G-districts/CrowPanel-7.0-HMI-ESP32-Display-800x480/example/V1.0_and_V2.0/Arduino/arduino_code/7.0libraries/ESP32-audioI2S-master/examples/ESP32_A1S/AI-Thinker ESP32-Audio-Kit.jpg

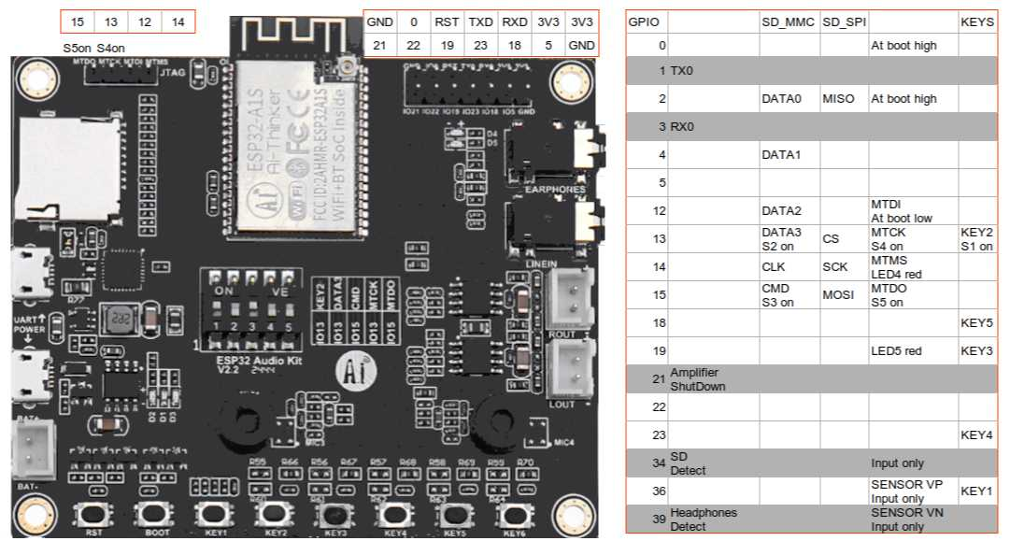
example/V1.0_and_V2.0/Arduino/arduino_code/7.0libraries/ESP32-audioI2S-master/examples/ESP32_A1S/AI-Thinker ESP32-Audio-Kit.jpg
