G-districts/CrowPanel-7.0-HMI-ESP32-Display-800x480/example/V1.0_and_V2.0/Arduino/arduino_code/7.0libraries/ESP32-audioI2S-master/examples/Simple_WiFi_Radio/Simple_WiFi_Radio_3.jpg

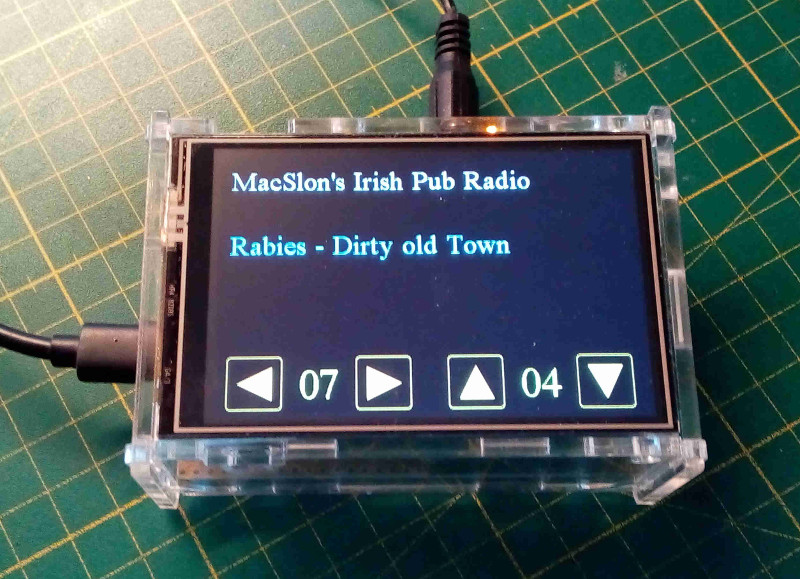
example/V1.0_and_V2.0/Arduino/arduino_code/7.0libraries/ESP32-audioI2S-master/examples/Simple_WiFi_Radio/Simple_WiFi_Radio_3.jpg
