G-districts/CrowPanel-7.0-HMI-ESP32-Display-800x480/example/V1.0_and_V2.0/HomeAssistant_7.0/7.0-inch_Squareline_Demo/README/2.png

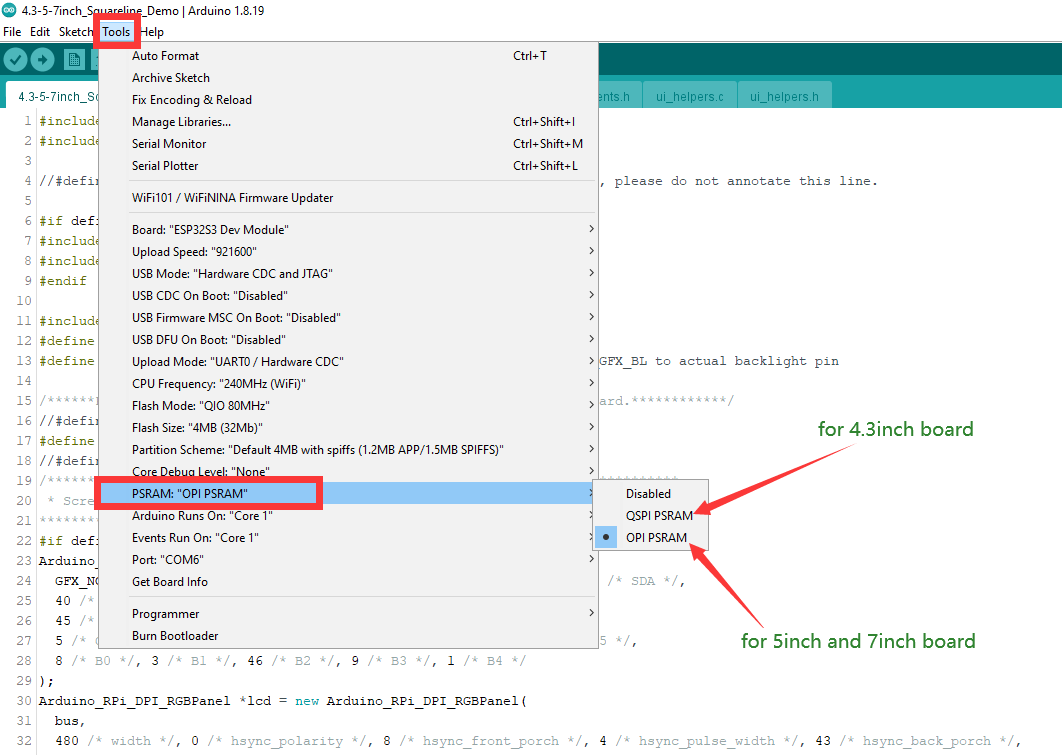
example/V1.0_and_V2.0/HomeAssistant_7.0/7.0-inch_Squareline_Demo/README/2.png
