G-districts/CrowPanel-7.0-HMI-ESP32-Display-800x480/example/V3.0/Micropython/SquareLine_Studio_Demo/LVGL-Assets-800x480/background1.png

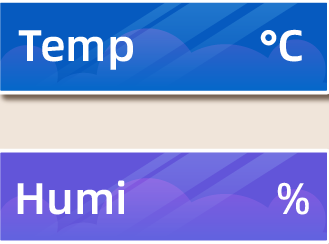
example/V3.0/Micropython/SquareLine_Studio_Demo/LVGL-Assets-800x480/background1.png
