G-districts/CrowPanel-7.0-HMI-ESP32-Display-800x480/example/V3.0/PlatformIO/LVGL-Assets-800x480/background.png

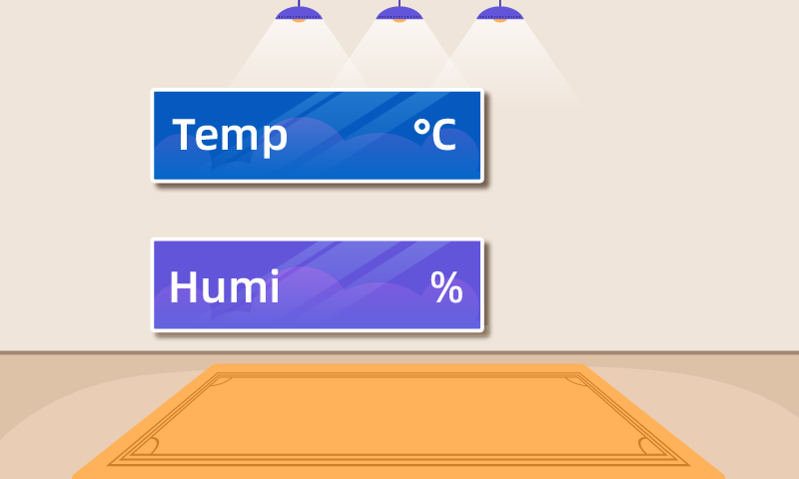
example/V3.0/PlatformIO/LVGL-Assets-800x480/background.png
