G-districts/CrowPanel-7.0-HMI-ESP32-Display-800x480/example/V3.0/ESP_IDF/LVGL_IDF/components/Arduino_GFX-master/examples/ImgViewer/ImgViewerBmp/data/octocatL.bmp

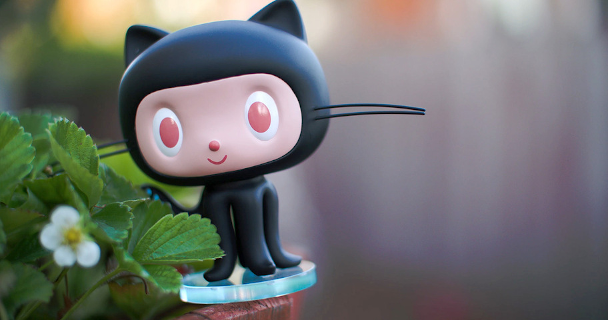
example/V3.0/ESP_IDF/LVGL_IDF/components/Arduino_GFX-master/examples/ImgViewer/ImgViewerBmp/data/octocatL.bmp
