G-districts/CrowPanel-7.0-HMI-ESP32-Display-800x480/example/V3.0/ESP_IDF/LVGL_IDF/components/Arduino_GFX-master/examples/ImgViewer/ImgViewerPng_PNGdec/data/octocat.png

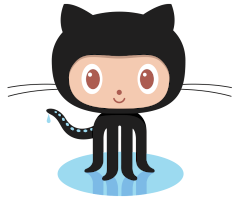
example/V3.0/ESP_IDF/LVGL_IDF/components/Arduino_GFX-master/examples/ImgViewer/ImgViewerPng_PNGdec/data/octocat.png
