G-districts/CrowPanel-7.0-HMI-ESP32-Display-800x480/example/V3.0/ESP_IDF/LVGL_IDF/components/Arduino_GFX-master/examples/ImgViewer/ImgViewerTiff_G4/data/at3_1m4_01_g4.tif

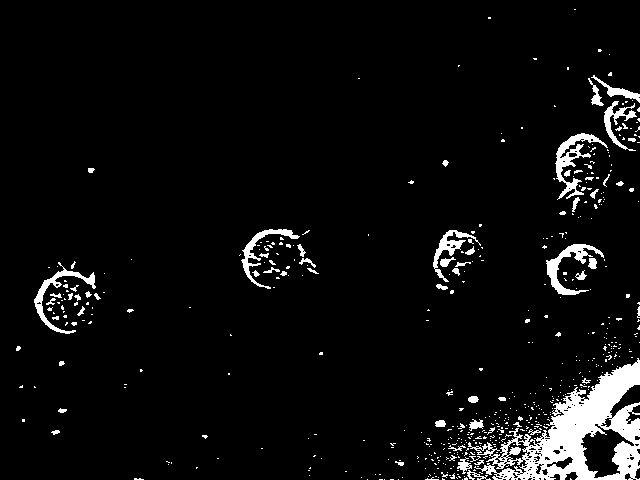
example/V3.0/ESP_IDF/LVGL_IDF/components/Arduino_GFX-master/examples/ImgViewer/ImgViewerTiff_G4/data/at3_1m4_01_g4.tif
