G-districts/CrowPanel-7.0-HMI-ESP32-Display-800x480/example/V3.0/ESP_IDF/LVGL_IDF/components/Arduino_GFX-master/examples/Sprite/SpriteGif/data/city17_240.gif

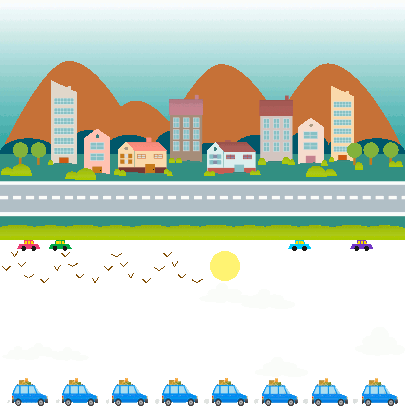
example/V3.0/ESP_IDF/LVGL_IDF/components/Arduino_GFX-master/examples/Sprite/SpriteGif/data/city17_240.gif
