G-districts/CrowPanel-7.0-HMI-ESP32-Display-800x480/example/V3.0/ESP_IDF/LVGL_IDF/components/Arduino_GFX-master/src/display/Arduino_RGB_Display.h

#pragma once

#include "../Arduino_DataBus.h"

//#if defined(ESP32) && (CONFIG_IDF_TARGET_ESP32S3)
#if defined(ESP32) && (CONFIG_IDF_TARGET_ESP32S3 || CONFIG_IDF_TARGET_ESP32P4)  //Modify

#include "../Arduino_GFX.h"
#include "../databus/Arduino_ESP32RGBPanel.h"

static const uint8_t gc9503v_type1_init_operations[] = {
    BEGIN_WRITE,
    WRITE_COMMAND_8, 0xF0,
    WRITE_BYTES, 5, 0x55, 0xAA, 0x52, 0x08, 0x00,

    WRITE_C8_D16, 0xF6, 0x5A, 0x87,

    WRITE_C8_D8, 0xC1, 0x3F,
    WRITE_C8_D8, 0xC2, 0x0E,
    WRITE_C8_D8, 0xC6, 0xF8,
    WRITE_C8_D8, 0xC9, 0x10,
    WRITE_C8_D8, 0xCD, 0x25,
    WRITE_C8_D8, 0xF8, 0x8A,
    WRITE_C8_D8, 0xAC, 0x45,
    WRITE_C8_D8, 0xA0, 0xDD,
    WRITE_C8_D8, 0xA7, 0x47,

    WRITE_COMMAND_8, 0xFA,
    WRITE_BYTES, 4, 0x00, 0x00, 0x00, 0x04,

    WRITE_C8_D8, 0xA3, 0xEE,

    WRITE_COMMAND_8, 0xFD,
    WRITE_BYTES, 3, 0x28, 0x28, 0x00,

    WRITE_C8_D8, 0x71, 0x48,
    WRITE_C8_D8, 0x72, 0x48,
    WRITE_C8_D16, 0x73, 0x00, 0x44,
    WRITE_C8_D8, 0x97, 0xEE,
    WRITE_C8_D8, 0x83, 0x93,
    WRITE_C8_D8, 0x9A, 0x72,
    WRITE_C8_D8, 0x9B, 0x5a,
    WRITE_C8_D16, 0x82, 0x2c, 0x2c,
    WRITE_C8_D8, 0xB1, 0x10,

    WRITE_COMMAND_8, 0x6D,
    WRITE_BYTES, 32,
    0x00, 0x1F, 0x19, 0x1A,
    0x10, 0x0e, 0x0c, 0x0a,
    0x02, 0x07, 0x1E, 0x1E,
    0x1E, 0x1E, 0x1E, 0x1E,
    0x1E, 0x1E, 0x1E, 0x1E,
    0x1E, 0x1E, 0x08, 0x01,
    0x09, 0x0b, 0x0D, 0x0F,
    0x1a, 0x19, 0x1f, 0x00,

    WRITE_COMMAND_8, 0x64,
    WRITE_BYTES, 16,
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

    WRITE_COMMAND_8, 0xEB,
    WRITE_BYTES, 7,
    0x02, 0x01, 0xE4, 0xE4,
    0x44, 0x00, 0x40,

    WRITE_C8_D16, 0xEC, 0x02, 0x01,

    WRITE_COMMAND_8, 0xED,
    WRITE_BYTES, 16,
    0xAB, 0x89, 0x76, 0x54,
    0x01, 0xFF, 0xFF, 0xFF,
    0xFF, 0xFF, 0xFF, 0x10,
    0x45, 0x67, 0x98, 0xBA,

    //-----------------------------------------End GIP Setting-----------------------------------------//
    //--------------------------- Power Control Registers Initial End------------------------------//
    //-------------------------------------Bank1 Setting------------------------------------------------//
    WRITE_COMMAND_8, 0xFF,
    WRITE_BYTES, 5, 0x77, 0x01, 0x00, 0x00, 0x00,

    WRITE_COMMAND_8, 0x21,   // 0x20 normal, 0x21 IPS
    WRITE_C8_D8, 0x3A, 0x77, // RGB 24bits D[23:0]

    WRITE_COMMAND_8, 0x11, // Sleep Out
    END_WRITE,

    DELAY, 100,

    BEGIN_WRITE,
    WRITE_COMMAND_8, 0x29, // Display On
    END_WRITE};

static const uint8_t st7701_type3_init_operations[] = {
    BEGIN_WRITE,
    WRITE_COMMAND_8, 0xFF,
    WRITE_BYTES, 5, 0x77, 0x01, 0x00, 0x00, 0x10,

    WRITE_C8_D16, 0xC0, 0x3B, 0x00,
    WRITE_C8_D16, 0xC1, 0x0B, 0x02, // VBP
    WRITE_C8_D16, 0xC2, 0x00, 0x02,
    WRITE_C8_D8, 0xCC, 0x10,
    WRITE_C8_D8, 0xCD, 0x08,

    WRITE_COMMAND_8, 0xB0, // Positive Voltage Gamma Control
    WRITE_BYTES, 16,
    0x02, 0x13, 0x1B, 0x0D,
    0x10, 0x05, 0x08, 0x07,
    0x07, 0x24, 0x04, 0x11,
    0x0E, 0x2C, 0x33, 0x1D,

    WRITE_COMMAND_8, 0xB1, // Negative Voltage Gamma Control
    WRITE_BYTES, 16,
    0x05, 0x13, 0x1B, 0x0D,
    0x11, 0x05, 0x08, 0x07,
    0x07, 0x24, 0x04, 0x11,
    0x0E, 0x2C, 0x33, 0x1D,

    // PAGE1
    WRITE_COMMAND_8, 0xFF,
    WRITE_BYTES, 5, 0x77, 0x01, 0x00, 0x00, 0x11,

    WRITE_C8_D8, 0xB0, 0x5d, // 5d
    WRITE_C8_D8, 0xB1, 0x43, // VCOM amplitude setting
    WRITE_C8_D8, 0xB2, 0x81, // VGH Voltage setting, 12V
    WRITE_C8_D8, 0xB3, 0x80,
    WRITE_C8_D8, 0xB5, 0x43, // VGL Voltage setting, -8.3V
    WRITE_C8_D8, 0xB7, 0x85,
    WRITE_C8_D8, 0xB8, 0x20,

    WRITE_C8_D8, 0xC1, 0x78,
    WRITE_C8_D8, 0xC2, 0x78,

    WRITE_C8_D8, 0xD0, 0x88,

    WRITE_COMMAND_8, 0xE0,
    WRITE_BYTES, 3, 0x00, 0x00, 0x02,

    WRITE_COMMAND_8, 0xE1,
    WRITE_BYTES, 11,
    0x03, 0xA0, 0x00, 0x00,
    0x04, 0xA0, 0x00, 0x00,
    0x00, 0x20, 0x20,

    WRITE_COMMAND_8, 0xE2,
    WRITE_BYTES, 12,
    0x00, 0x00, 0x00, 0x00,
    0x00, 0x00, 0x00, 0x00,
    0x00, 0x00, 0x00, 0x00,

    WRITE_COMMAND_8, 0xE3,
    WRITE_BYTES, 4, 0x00, 0x00, 0x11, 0x00,

    WRITE_C8_D16, 0xE4, 0x22, 0x00,

    WRITE_COMMAND_8, 0xE5,
    WRITE_BYTES, 16,
    0x05, 0xEC, 0xA0, 0xA0,
    0x07, 0xEE, 0xA0, 0xA0,
    0x00, 0x00, 0x00, 0x00,
    0x00, 0x00, 0x00, 0x00,

    WRITE_COMMAND_8, 0xE6,
    WRITE_BYTES, 4, 0x00, 0x00, 0x11, 0x00,

    WRITE_C8_D16, 0xE7, 0x22, 0x00,

    WRITE_COMMAND_8, 0xE8,
    WRITE_BYTES, 16,
    0x06, 0xED, 0xA0, 0xA0,
    0x08, 0xEF, 0xA0, 0xA0,
    0x00, 0x00, 0x00, 0x00,
    0x00, 0x00, 0x00, 0x00,

    WRITE_COMMAND_8, 0xEB,
    WRITE_BYTES, 7,
    0x00, 0x00, 0x40, 0x40,
    0x00, 0x00, 0x00,

    WRITE_COMMAND_8, 0xED,
    WRITE_BYTES, 16,
    0xFF, 0xFF, 0xFF, 0xBA,
    0x0A, 0xBF, 0x45, 0xFF,
    0xFF, 0x54, 0xFB, 0xA0,
    0xAB, 0xFF, 0xFF, 0xFF,

    WRITE_COMMAND_8, 0xEF,
    WRITE_BYTES, 6,
    0x10, 0x0D, 0x04, 0x08,
    0x3F, 0x1F,

    WRITE_COMMAND_8, 0xFF,
    WRITE_BYTES, 5, 0x77, 0x01, 0x00, 0x00, 0x13,

    WRITE_C8_D8, 0xEF, 0x08,

    WRITE_COMMAND_8, 0xFF,
    WRITE_BYTES, 5, 0x77, 0x01, 0x00, 0x00, 0x00,

    WRITE_COMMAND_8, 0x11, // Sleep Out
    END_WRITE,

    DELAY, 120,

    BEGIN_WRITE,
    WRITE_COMMAND_8, 0x29,   // Display On
    WRITE_COMMAND_8, 0x21,   // 0x20 normal, 0x21 IPS
    WRITE_C8_D8, 0x36, 0x00, // Display data access control
    WRITE_C8_D8, 0x3A, 0x60, // 0x60 18bit   0x50 16bit
    END_WRITE};

static const uint8_t st7701_type4_init_operations[] = {
    BEGIN_WRITE,

    WRITE_COMMAND_8, 0xFF,
    WRITE_BYTES, 5, 0x77, 0x01, 0x00, 0x00, 0x10,

    WRITE_C8_D16, 0xC0, 0x3b, 0x00,
    WRITE_C8_D16, 0xC1, 0x0b, 0x02,
    WRITE_C8_D16, 0xC2, 0x07, 0x02,
    WRITE_C8_D8, 0xCC, 0x10,
    WRITE_C8_D8, 0xCD, 0x08,

    WRITE_COMMAND_8, 0xB0, // Positive Voltage Gamma Control
    WRITE_BYTES, 16,
    0x00, 0x11, 0x16, 0x0e,
    0x11, 0x06, 0x05, 0x09,
    0x08, 0x21, 0x06, 0x13,
    0x10, 0x29, 0x31, 0x18,

    WRITE_COMMAND_8, 0xB1, // Negative Voltage Gamma Control
    WRITE_BYTES, 16,
    0x00, 0x11, 0x16, 0x0e,
    0x11, 0x07, 0x05, 0x09,
    0x09, 0x21, 0x05, 0x13,
    0x11, 0x2a, 0x31, 0x18,

    WRITE_COMMAND_8, 0xFF,
    WRITE_BYTES, 5, 0x77, 0x01, 0x00, 0x00, 0x11,

    WRITE_C8_D8, 0xb0, 0x6d,
    WRITE_C8_D8, 0xb1, 0x37,
    WRITE_C8_D8, 0xb2, 0x81,
    WRITE_C8_D8, 0xb3, 0x80,
    WRITE_C8_D8, 0xb5, 0x43,
    WRITE_C8_D8, 0xb7, 0x85,
    WRITE_C8_D8, 0xb8, 0x20,

    WRITE_C8_D8, 0xc1, 0x78,
    WRITE_C8_D8, 0xc2, 0x78,
    WRITE_C8_D8, 0xc3, 0x8c,

    WRITE_C8_D8, 0xd0, 0x88,

    WRITE_COMMAND_8, 0xe0,
    WRITE_BYTES, 3, 0x00, 0x00, 0x02,
    WRITE_COMMAND_8, 0xe1,
    WRITE_BYTES, 11,
    0x03, 0xa0, 0x00, 0x00,
    0x04, 0xa0, 0x00, 0x00,
    0x00, 0x20, 0x20,
    WRITE_COMMAND_8, 0xe2,
    WRITE_BYTES, 13,
    0x00, 0x00, 0x00, 0x00,
    0x00, 0x00, 0x00, 0x00,
    0x00, 0x00, 0x00, 0x00,
    0x00,
    WRITE_COMMAND_8, 0xe3,
    WRITE_BYTES, 4, 0x00, 0x00, 0x11, 0x00,
    WRITE_C8_D16, 0xe4, 0x22, 0x00,
    WRITE_COMMAND_8, 0xe5,
    WRITE_BYTES, 16,
    0x05, 0xec, 0xa0, 0xa0,
    0x07, 0xee, 0xa0, 0xa0,
    0x00, 0x00, 0x00, 0x00,
    0x00, 0x00, 0x00, 0x00,
    WRITE_COMMAND_8, 0xe6,
    WRITE_BYTES, 4, 0x00, 0x00, 0x11, 0x00,
    WRITE_C8_D16, 0xe7, 0x22, 0x00,
    WRITE_COMMAND_8, 0xe8,
    WRITE_BYTES, 16,
    0x06, 0xed, 0xa0, 0xa0,
    0x08, 0xef, 0xa0, 0xa0,
    0x00, 0x00, 0x00, 0x00,
    0x00, 0x00, 0x00, 0x00,
    WRITE_COMMAND_8, 0xeb,
    WRITE_BYTES, 7,
    0x00, 0x00, 0x40, 0x40,
    0x00, 0x00, 0x00,
    WRITE_COMMAND_8, 0xed,
    WRITE_BYTES, 16,
    0xff, 0xff, 0xff, 0xba,
    0x0a, 0xbf, 0x45, 0xff,
    0xff, 0x54, 0xfb, 0xa0,
    0xab, 0xff, 0xff, 0xff,
    WRITE_COMMAND_8, 0xef,
    WRITE_BYTES, 6,
    0x10, 0x0d, 0x04, 0x08,
    0x3f, 0x1f,
    WRITE_COMMAND_8, 0xff,
    WRITE_BYTES, 5, 0x77, 0x01, 0x00, 0x00, 0x13,
    WRITE_C8_D8, 0xef, 0x08,
    WRITE_COMMAND_8, 0xff,
    WRITE_BYTES, 5, 0x77, 0x01, 0x00, 0x00, 0x00,
    WRITE_C8_D8, 0x36, 0x08,
    WRITE_C8_D8, 0x3a, 0x66,
    WRITE_C8_D8, 0x11, 0x00,
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

    WRITE_C8_D8, 0xC1, 0x78,
    WRITE_C8_D8, 0xC2, 0x78,

    WRITE_C8_D8, 0xD0, 0x88,

    WRITE_C8_D8, 0xE0, 0x00,

    WRITE_C8_D8, 0x1B, 0x02,

    WRITE_COMMAND_8, 0xE1,
    WRITE_BYTES, 11,
    0x08, 0xA0, 0x00, 0x00,
    0x07, 0xA0, 0x00, 0x00,
    0x00, 0x44, 0x44,

    WRITE_COMMAND_8, 0xE2,
    WRITE_BYTES, 12,
    0x11, 0x11, 0x44, 0x44,
    0x75, 0xA0, 0x00, 0x00,
    0x74, 0xA0, 0x00, 0x00,

    WRITE_COMMAND_8, 0xE3,
    WRITE_BYTES, 4, 0x00, 0x00, 0x11, 0x11,

    WRITE_C8_D16, 0xE4, 0x44, 0x44,

    WRITE_COMMAND_8, 0xE5,
    WRITE_BYTES, 16,
    0x0A, 0x71, 0xD8, 0xA0,
    0x0C, 0x73, 0xD8, 0xA0,
    0x0E, 0x75, 0xD8, 0xA0,
    0x10, 0x77, 0xD8, 0xA0,

    WRITE_COMMAND_8, 0xE6,
    WRITE_BYTES, 4, 0x00, 0x00, 0x11, 0x11,

    WRITE_C8_D16, 0xE7, 0x44, 0x44,

    WRITE_COMMAND_8, 0xE8,
    WRITE_BYTES, 16,
    0x09, 0x70, 0xD8, 0xA0,
    0x0B, 0x72, 0xD8, 0xA0,
    0x0D, 0x74, 0xD8, 0xA0,
    0x0F, 0x76, 0xD8, 0xA0,

    WRITE_COMMAND_8, 0xEB,
    WRITE_BYTES, 7,
    0x02, 0x00, 0xE4, 0xE4,
    0x88, 0x00, 0x40,

    WRITE_C8_D16, 0xEC, 0x3C, 0x00,

    WRITE_COMMAND_8, 0xED,
    WRITE_BYTES, 16,
    0xAB, 0x89, 0x76, 0x54,
    0x02, 0xFF, 0xFF, 0xFF,
    0xFF, 0xFF, 0xFF, 0x20,
    0x45, 0x67, 0x98, 0xBA,

    WRITE_COMMAND_8, 0xEF,
    WRITE_BYTES, 6,
    0x08, 0x08, 0x08, 0x45,
    0x3F, 0x54,

    WRITE_COMMAND_8, 0xFF,
    WRITE_BYTES, 5, 0x77, 0x01, 0x00, 0x00, 0x13,

    WRITE_C8_D16, 0xE8, 0x00, 0x0E,

    WRITE_COMMAND_8, 0x20,   // 0x20 normal, 0x21 IPS
    WRITE_C8_D8, 0x3A, 0x50, // 0x70 RGB888, 0x60 RGB666, 0x50 RGB565

    WRITE_COMMAND_8, 0x11, // Sleep Out
    END_WRITE,

    DELAY, 150,

    BEGIN_WRITE,
    WRITE_C8_D16, 0xE8, 0x00, 0x0C,
    END_WRITE,

    DELAY, 100,

    BEGIN_WRITE,
    WRITE_C8_D16, 0xE8, 0x00, 0x00,

    WRITE_COMMAND_8, 0xFF,
    WRITE_BYTES, 5, 0x77, 0x01, 0x00, 0x00, 0x00,

    WRITE_COMMAND_8, 0x29, // Display On
    END_WRITE,
    DELAY, 20};

// Init code for 480x480 square (86 Box) GUITION ESP32-4848S040 display
static const uint8_t st7701_type9_init_operations[] = {
    BEGIN_WRITE,
    WRITE_COMMAND_8, 0xFF,
    WRITE_BYTES, 5, 0x77, 0x01, 0x00, 0x00, 0x10,

    WRITE_C8_D16, 0xC0, 0x3B, 0x00,
    WRITE_C8_D16, 0xC1, 0x0D, 0x02,
    WRITE_C8_D16, 0xC2, 0x31, 0x05,
    WRITE_C8_D8, 0xCD, 0x00, // changed by manufacture

    WRITE_COMMAND_8, 0xB0, // Positive Voltage Gamma Control
    WRITE_BYTES, 16,
    0x00, 0x11, 0x18, 0x0E,
    0x11, 0x06, 0x07, 0x08,
    0x07, 0x22, 0x04, 0x12,
    0x0F, 0xAA, 0x31, 0x18,

    WRITE_COMMAND_8, 0xB1, // Negative Voltage Gamma Control
    WRITE_BYTES, 16,
    0x00, 0x11, 0x19, 0x0E,
    0x12, 0x07, 0x08, 0x08,
    0x08, 0x22, 0x04, 0x11,
    0x11, 0xA9, 0x32, 0x18,

    // PAGE1
    WRITE_COMMAND_8, 0xFF,
    WRITE_BYTES, 5, 0x77, 0x01, 0x00, 0x00, 0x11,

    WRITE_C8_D8, 0xB0, 0x60, // Vop=4.7375v
    WRITE_C8_D8, 0xB1, 0x32, // VCOM=32
    WRITE_C8_D8, 0xB2, 0x07, // VGH=15v
    WRITE_C8_D8, 0xB3, 0x80,
    WRITE_C8_D8, 0xB5, 0x49, // VGL=-10.17v
    WRITE_C8_D8, 0xB7, 0x85,
    WRITE_C8_D8, 0xB8, 0x21, // AVDD=6.6 & AVCL=-4.6
    WRITE_C8_D8, 0xC1, 0x78,
    WRITE_C8_D8, 0xC2, 0x78,

    WRITE_COMMAND_8, 0xE0,
    WRITE_BYTES, 3, 0x00, 0x1B, 0x02,

    WRITE_COMMAND_8, 0xE1,
    WRITE_BYTES, 11,
    0x08, 0xA0, 0x00, 0x00,
    0x07, 0xA0, 0x00, 0x00,
    0x00, 0x44, 0x44,

    WRITE_COMMAND_8, 0xE2,
    WRITE_BYTES, 12,
    0x11, 0x11, 0x44, 0x44,
    0xED, 0xA0, 0x00, 0x00,
    0xEC, 0xA0, 0x00, 0x00,

    WRITE_COMMAND_8, 0xE3,
    WRITE_BYTES, 4, 0x00, 0x00, 0x11, 0x11,

    WRITE_C8_D16, 0xE4, 0x44, 0x44,

    WRITE_COMMAND_8, 0xE5,
    WRITE_BYTES, 16,
    0x0A, 0xE9, 0xD8, 0xA0,
    0x0C, 0xEB, 0xD8, 0xA0,
    0x0E, 0xED, 0xD8, 0xA0,
    0x10, 0xEF, 0xD8, 0xA0,

    WRITE_COMMAND_8, 0xE6,
    WRITE_BYTES, 4, 0x00, 0x00, 0x11, 0x11,

    WRITE_C8_D16, 0xE7, 0x44, 0x44,

    WRITE_COMMAND_8, 0xE8,
    WRITE_BYTES, 16,
    0x09, 0xE8, 0xD8, 0xA0,
    0x0B, 0xEA, 0xD8, 0xA0,
    0x0D, 0xEC, 0xD8, 0xA0,
    0x0F, 0xEE, 0xD8, 0xA0,

    WRITE_COMMAND_8, 0xEB,
    WRITE_BYTES, 7,
    0x02, 0x00, 0xE4, 0xE4,
    0x88, 0x00, 0x40,

    WRITE_C8_D16, 0xEC, 0x3C, 0x00,

    WRITE_COMMAND_8, 0xED,
    WRITE_BYTES, 16,
    0xAB, 0x89, 0x76, 0x54,
    0x02, 0xFF, 0xFF, 0xFF,
    0xFF, 0xFF, 0xFF, 0x20,
    0x45, 0x67, 0x98, 0xBA,

    //-----------VAP & VAN---------------
    WRITE_COMMAND_8, 0xFF,
    WRITE_BYTES, 5, 0x77, 0x01, 0x00, 0x00, 0x13,

    WRITE_C8_D8, 0xE5, 0xE4,

    WRITE_COMMAND_8, 0xFF,
    WRITE_BYTES, 5, 0x77, 0x01, 0x00, 0x00, 0x00,

    // WRITE_COMMAND_8, 0x21,   // 0x20 normal, 0x21 IPS // commented by manufacture
    WRITE_C8_D8, 0x3A, 0x60, // 0x70 RGB888, 0x60 RGB666, 0x50 RGB565

    WRITE_COMMAND_8, 0x11, // Sleep Out
    END_WRITE,

    DELAY, 120,

    BEGIN_WRITE,
    WRITE_COMMAND_8, 0x29, // Display On
    END_WRITE};

// Init code for 480x480 round TL021WVC02 display
static const uint8_t TL021WVC02_init_operations[] = {
    BEGIN_WRITE,
    WRITE_COMMAND_8, 0xFF,
    WRITE_BYTES, 5, 0x77, 0x01, 0x00, 0x00, 0x10,
    WRITE_C8_D16, 0xC0, 0x3B, 0x00,
    WRITE_C8_D16, 0xC1, 0x0B, 0x02, // VBP
    WRITE_C8_D16, 0xC2, 0x00, 0x02,
    WRITE_C8_D8, 0xCC, 0x10,
    WRITE_C8_D8, 0xCD, 0x08,
    WRITE_COMMAND_8, 0xB0, // Positive Voltage Gamma Control
    WRITE_BYTES, 16,
    0x02, 0x13, 0x1B, 0x0D,
    0x10, 0x05, 0x08, 0x07,
    0x07, 0x24, 0x04, 0x11,
    0x0E, 0x2C, 0x33, 0x1D,

    WRITE_COMMAND_8, 0xB1, // Negative Voltage Gamma Control
    WRITE_BYTES, 16,
    0x05, 0x13, 0x1B, 0x0D,
    0x11, 0x05, 0x08, 0x07,
    0x07, 0x24, 0x04, 0x11,
    0x0E, 0x2C, 0x33, 0x1D,

    WRITE_COMMAND_8, 0xFF,
    WRITE_BYTES, 5, 0x77, 0x01, 0x00, 0x00, 0x11,

    WRITE_C8_D8, 0xB0, 0x5d, // 5d
    WRITE_C8_D8, 0xB1, 0x43, // VCOM amplitude setting
    WRITE_C8_D8, 0xB2, 0x81, // VGH Voltage setting, 12V
    WRITE_C8_D8, 0xB3, 0x80,

    WRITE_C8_D8, 0xB5, 0x43, // VGL Voltage setting, -8.3V

    WRITE_C8_D8, 0xB7, 0x85,
    WRITE_C8_D8, 0xB8, 0x20,

    WRITE_C8_D8, 0xC1, 0x78,
    WRITE_C8_D8, 0xC2, 0x78,

    WRITE_C8_D8, 0xD0, 0x88,

    WRITE_COMMAND_8, 0xE0,
    WRITE_BYTES, 3, 0x00, 0x00, 0x02,

    WRITE_COMMAND_8, 0xE1,
    WRITE_BYTES, 11,
    0x03, 0xA0, 0x00, 0x00,
    0x04, 0xA0, 0x00, 0x00,
    0x00, 0x20, 0x20,

    WRITE_COMMAND_8, 0xE2,
    WRITE_BYTES, 13,
    0x00, 0x00, 0x00, 0x00,
    0x00, 0x00, 0x00, 0x00,
    0x00, 0x00, 0x00, 0x00,
    0x00,

    WRITE_COMMAND_8, 0xE3,
    WRITE_BYTES, 4, 0x00, 0x00, 0x11, 0x00,

    WRITE_C8_D16, 0xE4, 0x22, 0x00,

    WRITE_COMMAND_8, 0xE5,
    WRITE_BYTES, 16,
    0x05, 0xEC, 0xA0, 0xA0,
    0x07, 0xEE, 0xA0, 0xA0,
    0x00, 0x00, 0x00, 0x00,
    0x00, 0x00, 0x00, 0x00,

    WRITE_COMMAND_8, 0xE6,
    WRITE_BYTES, 4, 0x00, 0x00, 0x11, 0x00,

    WRITE_C8_D16, 0xE7, 0x22, 0x00,

    WRITE_COMMAND_8, 0xE8,
    WRITE_BYTES, 16,
    0x06, 0xED, 0xA0, 0xA0,
    0x08, 0xEF, 0xA0, 0xA0,
    0x00, 0x00, 0x00, 0x00,
    0x00, 0x00, 0x00, 0x00,

    WRITE_COMMAND_8, 0xEB,
    WRITE_BYTES, 7,
    0x00, 0x00, 0x40, 0x40,
    0x00, 0x00, 0x00,

    WRITE_COMMAND_8, 0xED,
    WRITE_BYTES, 16,
    0xFF, 0xFF, 0xFF, 0xBA,
    0x0A, 0xBF, 0x45, 0xFF,
    0xFF, 0x54, 0xFB, 0xA0,
    0xAB, 0xFF, 0xFF, 0xFF,

    WRITE_COMMAND_8, 0xEF,
    WRITE_BYTES, 6,
    0x10, 0x0D, 0x04, 0x08,
    0x3F, 0x1F,

    WRITE_COMMAND_8, 0xFF,
    WRITE_BYTES, 5, 0x77, 0x01, 0x00, 0x00, 0x13,

    WRITE_C8_D8, 0xEF, 0x08,

    WRITE_COMMAND_8, 0xFF,
    WRITE_BYTES, 5, 0x77, 0x01, 0x00, 0x00, 0x00,

    WRITE_C8_D8, 0x36, 0x00,
    WRITE_C8_D8, 0x3A, 0x60, // 0x70 RGB888, 0x60 RGB666, 0x50 RGB565

    WRITE_COMMAND_8, 0x11, // Sleep Out
    END_WRITE,

    DELAY, 100,

    BEGIN_WRITE,
    WRITE_COMMAND_8, 0x29, // Display On
    END_WRITE,

    DELAY, 50};

// HD40015C40-Y
//    1 /* hync_polarity */, 46 /* hsync_front_porch */, 2 /* hsync_pulse_width */, 44 /* hsync_back_porch */,
//    1 /* vsync_polarity */, 50 /* vsync_front_porch */, 16 /* vsync_pulse_width */, 16 /* vsync_back_porch */);
static const uint8_t hd40015c40_init_operations[] = {
    BEGIN_WRITE,
    WRITE_C8_D8, 0xFF, 0x30,
    WRITE_C8_D8, 0xFF, 0x52,
    WRITE_C8_D8, 0xFF, 0x01,
    WRITE_C8_D8, 0xE3, 0x00,
    WRITE_C8_D8, 0x0A, 0x11,
    WRITE_C8_D8, 0x23, 0xA0,
    WRITE_C8_D8, 0x24, 0x32,
    WRITE_C8_D8, 0x25, 0x12,
    WRITE_C8_D8, 0x26, 0x2E,
    WRITE_C8_D8, 0x27, 0x2E,
    WRITE_C8_D8, 0x29, 0x02,
    WRITE_C8_D8, 0x2A, 0xCF,
    WRITE_C8_D8, 0x32, 0x34,
    WRITE_C8_D8, 0x38, 0x9C,
    WRITE_C8_D8, 0x39, 0xA7,
    WRITE_C8_D8, 0x3A, 0x27,
    WRITE_C8_D8, 0x3B, 0x94,
    WRITE_C8_D8, 0x42, 0x6D,
    WRITE_C8_D8, 0x43, 0x83,
    WRITE_C8_D8, 0x81, 0x00,
    WRITE_C8_D8, 0x91, 0x67,
    WRITE_C8_D8, 0x92, 0x67,
    WRITE_C8_D8, 0xA0, 0x52,
    WRITE_C8_D8, 0xA1, 0x50,
    WRITE_C8_D8, 0xA4, 0x9C,
    WRITE_C8_D8, 0xA7, 0x02,
    WRITE_C8_D8, 0xA8, 0x02,
    WRITE_C8_D8, 0xA9, 0x02,
    WRITE_C8_D8, 0xAA, 0xA8,
    WRITE_C8_D8, 0xAB, 0x28,
    WRITE_C8_D8, 0xAE, 0xD2,
    WRITE_C8_D8, 0xAF, 0x02,
    WRITE_C8_D8, 0xB0, 0xD2,
    WRITE_C8_D8, 0xB2, 0x26,
    WRITE_C8_D8, 0xB3, 0x26,
    WRITE_C8_D8, 0xFF, 0x30,
    WRITE_C8_D8, 0xFF, 0x52,
    WRITE_C8_D8, 0xFF, 0x02,
    WRITE_C8_D8, 0xB1, 0x0A,
    WRITE_C8_D8, 0xD1, 0x0E,
    WRITE_C8_D8, 0xB4, 0x2F,
    WRITE_C8_D8, 0xD4, 0x2D,
    WRITE_C8_D8, 0xB2, 0x0C,
    WRITE_C8_D8, 0xD2, 0x0C,
    WRITE_C8_D8, 0xB3, 0x30,
    WRITE_C8_D8, 0xD3, 0x2A,
    WRITE_C8_D8, 0xB6, 0x1E,
    WRITE_C8_D8, 0xD6, 0x16,
    WRITE_C8_D8, 0xB7, 0x3B,
    WRITE_C8_D8, 0xD7, 0x35,
    WRITE_C8_D8, 0xC1, 0x08,
    WRITE_C8_D8, 0xE1, 0x08,
    WRITE_C8_D8, 0xB8, 0x0D,
    WRITE_C8_D8, 0xD8, 0x0D,
    WRITE_C8_D8, 0xB9, 0x05,
    WRITE_C8_D8, 0xD9, 0x05,
    WRITE_C8_D8, 0xBD, 0x15,
    WRITE_C8_D8, 0xDD, 0x15,
    WRITE_C8_D8, 0xBC, 0x13,
    WRITE_C8_D8, 0xDC, 0x13,
    WRITE_C8_D8, 0xBB, 0x12,
    WRITE_C8_D8, 0xDB, 0x10,
    WRITE_C8_D8, 0xBA, 0x11,
    WRITE_C8_D8, 0xDA, 0x11,
    WRITE_C8_D8, 0xBE, 0x17,
    WRITE_C8_D8, 0xDE, 0x17,
    WRITE_C8_D8, 0xBF, 0x0F,
    WRITE_C8_D8, 0xDF, 0x0F,
    WRITE_C8_D8, 0xC0, 0x16,
    WRITE_C8_D8, 0xE0, 0x16,
    WRITE_C8_D8, 0xB5, 0x2E,
    WRITE_C8_D8, 0xD5, 0x3F,
    WRITE_C8_D8, 0xB0, 0x03,
    WRITE_C8_D8, 0xD0, 0x02,
    WRITE_C8_D8, 0xFF, 0x30,
    WRITE_C8_D8, 0xFF, 0x52,
    WRITE_C8_D8, 0xFF, 0x03,
    WRITE_C8_D8, 0x08, 0x09,
    WRITE_C8_D8, 0x09, 0x0A,
    WRITE_C8_D8, 0x0A, 0x0B,
    WRITE_C8_D8, 0x0B, 0x0C,
    WRITE_C8_D8, 0x28, 0x22,
    WRITE_C8_D8, 0x2A, 0xE9,
    WRITE_C8_D8, 0x2B, 0xE9,
    WRITE_C8_D8, 0x34, 0x51,
    WRITE_C8_D8, 0x35, 0x01,
    WRITE_C8_D8, 0x36, 0x26,
    WRITE_C8_D8, 0x37, 0x13,
    WRITE_C8_D8, 0x40, 0x07,
    WRITE_C8_D8, 0x41, 0x08,
    WRITE_C8_D8, 0x42, 0x09,
    WRITE_C8_D8, 0x43, 0x0A,
    WRITE_C8_D8, 0x44, 0x22,
    WRITE_C8_D8, 0x45, 0xDB,
    WRITE_C8_D8, 0x46, 0xdC,
    WRITE_C8_D8, 0x47, 0x22,
    WRITE_C8_D8, 0x48, 0xDD,
    WRITE_C8_D8, 0x49, 0xDE,
    WRITE_C8_D8, 0x50, 0x0B,
    WRITE_C8_D8, 0x51, 0x0C,
    WRITE_C8_D8, 0x52, 0x0D,
    WRITE_C8_D8, 0x53, 0x0E,
    WRITE_C8_D8, 0x54, 0x22,
    WRITE_C8_D8, 0x55, 0xDF,
    WRITE_C8_D8, 0x56, 0xE0,
    WRITE_C8_D8, 0x57, 0x22,
    WRITE_C8_D8, 0x58, 0xE1,
    WRITE_C8_D8, 0x59, 0xE2,
    WRITE_C8_D8, 0x80, 0x1E,
    WRITE_C8_D8, 0x81, 0x1E,
    WRITE_C8_D8, 0x82, 0x1F,
    WRITE_C8_D8, 0x83, 0x1F,
    WRITE_C8_D8, 0x84, 0x05,
    WRITE_C8_D8, 0x85, 0x0A,
    WRITE_C8_D8, 0x86, 0x0A,
    WRITE_C8_D8, 0x87, 0x0C,
    WRITE_C8_D8, 0x88, 0x0C,
    WRITE_C8_D8, 0x89, 0x0E,
    WRITE_C8_D8, 0x8A, 0x0E,
    WRITE_C8_D8, 0x8B, 0x10,
    WRITE_C8_D8, 0x8C, 0x10,
    WRITE_C8_D8, 0x8D, 0x00,
    WRITE_C8_D8, 0x8E, 0x00,
    WRITE_C8_D8, 0x8F, 0x1F,
    WRITE_C8_D8, 0x90, 0x1F,
    WRITE_C8_D8, 0x91, 0x1E,
    WRITE_C8_D8, 0x92, 0x1E,
    WRITE_C8_D8, 0x93, 0x02,
    WRITE_C8_D8, 0x94, 0x04,
    WRITE_C8_D8, 0x96, 0x1E,
    WRITE_C8_D8, 0x97, 0x1E,
    WRITE_C8_D8, 0x98, 0x1F,
    WRITE_C8_D8, 0x99, 0x1F,
    WRITE_C8_D8, 0x9A, 0x05,
    WRITE_C8_D8, 0x9B, 0x09,
    WRITE_C8_D8, 0x9C, 0x09,
    WRITE_C8_D8, 0x9D, 0x0B,
    WRITE_C8_D8, 0x9E, 0x0B,
    WRITE_C8_D8, 0x9F, 0x0D,
    WRITE_C8_D8, 0xA0, 0x0D,
    WRITE_C8_D8, 0xA1, 0x0F,
    WRITE_C8_D8, 0xA2, 0x0F,
    WRITE_C8_D8, 0xA3, 0x00,
    WRITE_C8_D8, 0xA4, 0x00,
    WRITE_C8_D8, 0xA5, 0x1F,
    WRITE_C8_D8, 0xA6, 0x1F,
    WRITE_C8_D8, 0xA7, 0x1E,
    WRITE_C8_D8, 0xA8, 0x1E,
    WRITE_C8_D8, 0xA9, 0x01,
    WRITE_C8_D8, 0xAA, 0x03,

    WRITE_C8_D8, 0xFF, 0x30,
    WRITE_C8_D8, 0xFF, 0x52,
    WRITE_C8_D8, 0xFF, 0x00,
    WRITE_C8_D8, 0x36, 0x0A,

    WRITE_COMMAND_8, 0x11, // Sleep Out
    END_WRITE,

    DELAY, 100,

    BEGIN_WRITE,
    WRITE_COMMAND_8, 0x29, // Display On
    END_WRITE,

    DELAY, 50};

// TL034WVS05-B1477A 3.4" 480x480 square display
static const uint8_t tl034wvs05_b1477a_init_operations[] = {
    BEGIN_WRITE,

    WRITE_COMMAND_8, 0xFF,
    WRITE_BYTES, 5,
    0x77, 0x01, 0x00, 0x00, 0x13,
    WRITE_C8_D8, 0xEF, 0x08,

    WRITE_COMMAND_8, 0xFF,
    WRITE_BYTES, 5,
    0x77, 0x01, 0x00, 0x00, 0x10,

    WRITE_C8_D16, 0xC0, 0x3B, 0x00,
    WRITE_C8_D16, 0xC1, 0x12, 0x0A,
    WRITE_C8_D16, 0xC2, 0x07, 0x03,
    WRITE_C8_D8, 0xC3, 0x02, // 80£ºHV mode
    WRITE_C8_D8, 0xCC, 0x10,
    WRITE_C8_D8, 0xCD, 0x08,

    WRITE_COMMAND_8, 0xB0,
    WRITE_BYTES, 16,
    0x0F, 0x11, 0x17, 0x15,
    0x15, 0x09, 0x0C, 0x08,
    0x08, 0x26, 0x04, 0x59,
    0x16, 0x66, 0x2D, 0x1F,
    WRITE_COMMAND_8, 0xB1,
    WRITE_BYTES, 16,
    0x0F, 0x11, 0x17, 0x15,
    0x15, 0x09, 0x0C, 0x08,
    0x08, 0x26, 0x04, 0x59,
    0x16, 0x66, 0x2D, 0x1F,

    WRITE_COMMAND_8, 0xFF,
    WRITE_BYTES, 5,
    0x77, 0x01, 0x00, 0x00, 0x11,

    WRITE_C8_D8, 0xB0, 0x6D,
    WRITE_C8_D8, 0xB1, 0x3A, // 30/47
    WRITE_C8_D8, 0xB2, 0x01,
    WRITE_C8_D8, 0xB3, 0x80,
    WRITE_C8_D8, 0xB5, 0x49,
    WRITE_C8_D8, 0xB7, 0x85,
    WRITE_C8_D8, 0xB8, 0x20,
    WRITE_C8_D8, 0xC1, 0x78,
    WRITE_C8_D8, 0xC2, 0x78,
    WRITE_C8_D8, 0xD0, 0x88,

    WRITE_COMMAND_8, 0xE0,
    WRITE_BYTES, 3, 0x00, 0x00, 0x02,

    WRITE_COMMAND_8, 0xE1,
    WRITE_BYTES, 11,
    0x07, 0x00, 0x09, 0x00,
    0x06, 0x00, 0x08, 0x00,
    0x00, 0x33, 0x33,

    WRITE_COMMAND_8, 0xE2,
    WRITE_BYTES, 13,
    0x11, 0x11, 0x33, 0x33,
    0xF6, 0x00, 0xF6, 0x00,
    0xF6, 0x00, 0xF6, 0x00,
    0x00,

    WRITE_COMMAND_8, 0xE3,
    WRITE_BYTES, 4,
    0x00, 0x00, 0x11, 0x11,

    WRITE_C8_D16, 0xE4, 0x44, 0x44,

    WRITE_COMMAND_8, 0xE5,
    WRITE_BYTES, 16,
    0x0F, 0xF3, 0x3D, 0xFF,
    0x11, 0xF5, 0x3D, 0xFF,
    0x0B, 0xEF, 0x3D, 0xFF,
    0x0D, 0xF1, 0x3D, 0xFF,

    WRITE_COMMAND_8, 0xE6,
    WRITE_BYTES, 4,
    0x00, 0x00, 0x11, 0x11,

    WRITE_C8_D16, 0xE7, 0x44, 0x44,

    WRITE_COMMAND_8, 0xE8,
    WRITE_BYTES, 16,
    0x0E, 0xF2, 0x3D, 0xFF,
    0x10, 0xF4, 0x3D, 0xFF,
    0x0A, 0xEE, 0x3D, 0xFF,
    0x0C, 0xF0, 0x3D, 0xFF,

    WRITE_C8_D16, 0xE9, 0x36, 0x00,

    WRITE_COMMAND_8, 0xEB,
    WRITE_BYTES, 7,
    0x00, 0x01, 0xE4, 0xE4,
    0x44, 0xAA, 0x10,

    WRITE_C8_D16, 0xEC, 0x3C, 0x00,

    WRITE_COMMAND_8, 0xED,
    WRITE_BYTES, 16,
    0xFF, 0x45, 0x67, 0xFA,
    0x01, 0x2B, 0xCF, 0xFF,
    0xFF, 0xFC, 0xB2, 0x10,
    0xAF, 0x76, 0x54, 0xFF,

    WRITE_COMMAND_8, 0xEF,
    WRITE_BYTES, 6,
    0x10, 0x0D, 0x04, 0x08, 0x3F, 0x1F,

    WRITE_COMMAND_8, 0xFF,
    WRITE_BYTES, 5,
    0x77, 0x01, 0x00, 0x00, 0x00,

    WRITE_C8_D8, 0x35, 0x00,
    WRITE_C8_D8, 0x3A, 0x66,

    WRITE_COMMAND_8, 0x11, // Sleep Out
    END_WRITE,

    DELAY, 120,

    BEGIN_WRITE,
    WRITE_COMMAND_8, 0x29, // Display On
    END_WRITE,

    DELAY, 50};

// TL032FWV01-I1440A 320 x 820 bar display
static const uint8_t tl032fwv01_init_operations[] = {
    BEGIN_WRITE,

    WRITE_COMMAND_8, 0x11, // Sleep Out

    END_WRITE,
    DELAY, 100,
    BEGIN_WRITE,

    WRITE_COMMAND_8, 0xFF,
    WRITE_BYTES, 5, 0x77, 0x01, 0x00, 0x00, 0x13,

    WRITE_C8_D8, 0xEF, 0x08,

    WRITE_COMMAND_8, 0xFF,
    WRITE_BYTES, 5, 0x77, 0x01, 0x00, 0x00, 0x10,

    WRITE_C8_D16, 0xC0, 0xE5, 0x02,

    WRITE_C8_D16, 0xC1, 0x0C, 0x0A, // VBP
    WRITE_C8_D16, 0xC2, 0x07, 0x0F,
    WRITE_C8_D8, 0xC2, 0x02,
    WRITE_C8_D8, 0xCC, 0x10,
    WRITE_C8_D8, 0xCD, 0x08,

    WRITE_COMMAND_8, 0xB0,
    WRITE_BYTES, 16,
    0x00, 0x08, 0x51, 0x0D,
    0xCE, 0x06, 0x00, 0x08,
    0x08, 0x1D, 0x02, 0xD0,
    0x0F, 0x6F, 0x36, 0x3F,

    WRITE_COMMAND_8, 0xB1,
    WRITE_BYTES, 16,
    0x00, 0x10, 0x4F, 0x0C,
    0x11, 0x05, 0x00, 0x07,
    0x07, 0x1F, 0x05, 0xD3,
    0x11, 0x6E, 0x34, 0x3F,

    WRITE_COMMAND_8, 0xFF,
    WRITE_BYTES, 5, 0x77, 0x01, 0x00, 0x00, 0x11,
    WRITE_C8_D8, 0xB0, 0x4D,
    WRITE_C8_D8, 0xB1, 0x1C,
    WRITE_C8_D8, 0xB2, 0x87,
    WRITE_C8_D8, 0xB3, 0x80,
    WRITE_C8_D8, 0xB5, 0x47,
    WRITE_C8_D8, 0xB7, 0x85,
    WRITE_C8_D8, 0xB8, 0x21,
    WRITE_C8_D8, 0xB9, 0x10,
    WRITE_C8_D8, 0xC1, 0x78,
    WRITE_C8_D8, 0xC2, 0x78,
    WRITE_C8_D8, 0xD0, 0x88,

    END_WRITE,
    DELAY, 100,
    BEGIN_WRITE,

    WRITE_COMMAND_8, 0xE0,
    WRITE_BYTES, 3,
    0x80, 0x00, 0x02,

    WRITE_COMMAND_8, 0xE1,
    WRITE_BYTES, 11,
    0x04, 0xA0, 0x00, 0x00,
    0x05, 0xA0, 0x00, 0x00,
    0x00, 0x60, 0x60,

    WRITE_COMMAND_8, 0xE2,
    WRITE_BYTES, 13,
    0x30, 0x30, 0x60, 0x60,
    0x3C, 0xA0, 0x00, 0x00,
    0x3D, 0xA0, 0x00, 0x00,
    0x00,

    WRITE_COMMAND_8, 0xE3,
    WRITE_BYTES, 4,
    0x00, 0x00, 0x33, 0x33,

    WRITE_C8_D16, 0xE4, 0x44, 0x44,

    WRITE_COMMAND_8, 0xE5,
    WRITE_BYTES, 16,
    0x06, 0x3E, 0xA0, 0xA0,
    0x08, 0x40, 0xA0, 0xA0,
    0x0A, 0x42, 0xA0, 0xA0,
    0x0C, 0x44, 0xA0, 0xA0,

    WRITE_COMMAND_8, 0xE6,
    WRITE_BYTES, 4,
    0x00, 0x00, 0x33, 0x33,

    WRITE_C8_D16, 0xE7, 0x44, 0x44,

    WRITE_COMMAND_8, 0xE8,
    WRITE_BYTES, 16,
    0x07, 0x3F, 0xA0, 0xA0,
    0x09, 0x41, 0xA0, 0xA0,
    0x0B, 0x43, 0xA0, 0xA0,
    0x0D, 0x45, 0xA0, 0xA0,

    WRITE_COMMAND_8, 0xEB,
    WRITE_BYTES, 7,
    0x00, 0x01, 0x4E, 0x4E,
    0xEE, 0x44, 0x00,

    WRITE_COMMAND_8, 0xED,
    WRITE_BYTES, 16,
    0xFF, 0xFF, 0x04, 0x56,
    0x72, 0xFF, 0xFF, 0xFF,
    0xFF, 0xFF, 0xFF, 0x27,
    0x65, 0x40, 0xFF, 0xFF,

    WRITE_COMMAND_8, 0xEF,
    WRITE_BYTES, 6,
    0x10, 0x0D, 0x04, 0x08, 0x3F, 0x1F,

    WRITE_COMMAND_8, 0xFF,
    WRITE_BYTES, 5,
    0x77, 0x01, 0x00, 0x00, 0x13,

    WRITE_C8_D16, 0xE8, 0x00, 0x0E,

    WRITE_COMMAND_8, 0xFF,
    WRITE_BYTES, 5,
    0x77, 0x01, 0x00, 0x00, 0x00,

    WRITE_COMMAND_8, 0x11,

    END_WRITE,
    DELAY, 120,
    BEGIN_WRITE,

    WRITE_COMMAND_8, 0xFF,
    WRITE_BYTES, 5,
    0x77, 0x01, 0x00, 0x00, 0x13,

    WRITE_C8_D16, 0xE8, 0x00, 0x0C,

    END_WRITE,
    DELAY, 10,
    BEGIN_WRITE,

    WRITE_C8_D16, 0xE8, 0x00, 0x00,
    WRITE_COMMAND_8, 0xFF,
    WRITE_BYTES, 5,
    0x77, 0x01, 0x00, 0x00, 0x00,

    WRITE_C8_D8, 0x36, 0x00,
    WRITE_C8_D8, 0x3A, 0x66,

    WRITE_COMMAND_8, 0x11,

    END_WRITE,
    DELAY, 120,
    BEGIN_WRITE,

    WRITE_COMMAND_8, 0x29,
    END_WRITE,
    DELAY, 120};

// TL040WVS03 480x480 4" square display
static const uint8_t tl040wvs03_init_operations[] = {
    BEGIN_WRITE,

    WRITE_COMMAND_8, 0xFF,
    WRITE_BYTES, 5, 0x77, 0x01, 0x00, 0x00, 0x10,

    WRITE_COMMAND_8, 0xC0,
    WRITE_BYTES, 2, 0x3B, 0x00,

    WRITE_COMMAND_8, 0xC1,
    WRITE_BYTES, 2, 0x0D, 0x02,

    WRITE_COMMAND_8, 0xC2,
    WRITE_BYTES, 2, 0x31, 0x05,

    WRITE_COMMAND_8, 0xCd,
    WRITE_BYTES, 1, 0x08,

    WRITE_COMMAND_8, 0xB0,
    WRITE_BYTES, 16, 0x00, 0x11, 0x18, 0x0E, 0x11, 0x06, 0x07, 0x08, 0x07, 0x22, 0x04, 0x12, 0x0F, 0xAA, 0x31, 0x18,

    WRITE_COMMAND_8, 0xB1,
    WRITE_BYTES, 16, 0x00, 0x11, 0x19, 0x0E, 0x12, 0x07, 0x08, 0x08, 0x08, 0x22, 0x04, 0x11, 0x11, 0xA9, 0x32, 0x18,

    WRITE_COMMAND_8, 0xFF,
    WRITE_BYTES, 5, 0x77, 0x01, 0x00, 0x00, 0x11,

    WRITE_COMMAND_8, 0xB0,
    WRITE_BYTES, 1, 0x60,

    WRITE_COMMAND_8, 0xB1,
    WRITE_BYTES, 1, 0x32,

    WRITE_COMMAND_8, 0xB2,
    WRITE_BYTES, 1, 0x07,

    WRITE_COMMAND_8, 0xB3,
    WRITE_BYTES, 1, 0x80,

    WRITE_COMMAND_8, 0xB5,
    WRITE_BYTES, 1, 0x49,

    WRITE_COMMAND_8, 0xB7,
    WRITE_BYTES, 1, 0x85,

    WRITE_COMMAND_8, 0xB8,
    WRITE_BYTES, 1, 0x21,

    WRITE_COMMAND_8, 0xC1,
    WRITE_BYTES, 1, 0x78,

    WRITE_COMMAND_8, 0xC2,
    WRITE_BYTES, 1, 0x78,

    WRITE_COMMAND_8, 0xE0,
    WRITE_BYTES, 3, 0x00, 0x1B, 0x02,

    WRITE_COMMAND_8, 0xE1,
    WRITE_BYTES, 11, 0x08, 0xA0, 0x00, 0x00, 0x07, 0xA0, 0x00, 0x00, 0x00, 0x44, 0x44,

    WRITE_COMMAND_8, 0xE2,
    WRITE_BYTES, 12, 0x11, 0x11, 0x44, 0x44, 0xED, 0xA0, 0x00, 0x00, 0xEC, 0xA0, 0x00, 0x00,

    WRITE_COMMAND_8, 0xE3,
    WRITE_BYTES, 4, 0x00, 0x00, 0x11, 0x11,

    WRITE_COMMAND_8, 0xE4,
    WRITE_BYTES, 2, 0x44, 0x44,

    WRITE_COMMAND_8, 0xE5,
    WRITE_BYTES, 16, 0x0A, 0xE9, 0xD8, 0xA0, 0x0C, 0xEB, 0xD8, 0xA0, 0x0E, 0xED, 0xD8, 0xA0, 0x10, 0xEF, 0xD8, 0xA0,

    WRITE_COMMAND_8, 0xE6,
    WRITE_BYTES, 4, 0x00, 0x00, 0x11, 0x11,

    WRITE_COMMAND_8, 0xE7,
    WRITE_BYTES, 2, 0x44, 0x44,

    WRITE_COMMAND_8, 0xE8,
    WRITE_BYTES, 16, 0x09, 0xE8, 0xD8, 0xA0, 0x0B, 0xEA, 0xD8, 0xA0, 0x0D, 0xEC, 0xD8, 0xA0, 0x0F, 0xEE, 0xD8, 0xA0,

    WRITE_COMMAND_8, 0xEB,
    WRITE_BYTES, 7, 0x02, 0x00, 0xE4, 0xE4, 0x88, 0x00, 0x40,

    WRITE_COMMAND_8, 0xEC,
    WRITE_BYTES, 2, 0x3C, 0x00,

    WRITE_COMMAND_8, 0xED,
    WRITE_BYTES, 16, 0xAB, 0x89, 0x76, 0x54, 0x02, 0xFF, 0xFF, 0xFF, 0xFF, 0xFF, 0xFF, 0x20, 0x45, 0x67, 0x98, 0xBA,

    WRITE_COMMAND_8, 0x36,
    WRITE_BYTES, 1, 0x00,

    WRITE_COMMAND_8, 0xFF,
    WRITE_BYTES, 5, 0x77, 0x01, 0x00, 0x00, 0x13,

    WRITE_COMMAND_8, 0xE5,
    WRITE_BYTES, 1, 0xE4,

    WRITE_COMMAND_8, 0xFF,
    WRITE_BYTES, 5, 0x77, 0x01, 0x00, 0x00, 0x00,

    WRITE_COMMAND_8, 0x3a,
    WRITE_BYTES, 1, 0x66,

    WRITE_COMMAND_8, 0x21,

    END_WRITE,
    DELAY, 10,
    BEGIN_WRITE,

    WRITE_COMMAND_8, 0x11,

    END_WRITE,
    DELAY, 120,
    BEGIN_WRITE,

    WRITE_COMMAND_8, 0x29,

    END_WRITE};

// TL028WVC01 2.8" round display
static const uint8_t TL028WVC01_init_operations[] = {
    BEGIN_WRITE,

    WRITE_COMMAND_8, 0xFF,
    WRITE_BYTES, 5,
    0x77, 0x01, 0x00, 0x00, 0x13,
    WRITE_C8_D8, 0xEF, 0x08,

    WRITE_COMMAND_8, 0xFF,
    WRITE_BYTES, 5,
    0x77, 0x01, 0x00, 0x00, 0x10,

    WRITE_C8_D16, 0xC0, 0x3B, 0x00,
    WRITE_C8_D16, 0xC1, 0x10, 0x0C,
    WRITE_C8_D16, 0xC2, 0x07, 0x0A,
    WRITE_C8_D8, 0xC7, 0x00,
    WRITE_C8_D8, 0xCC, 0x10,
    WRITE_C8_D8, 0xCD, 0x08,

    WRITE_COMMAND_8, 0xB0,
    WRITE_BYTES, 16,
    0x05, 0x12, 0x98, 0x0E, 0x0F, 0x07, 0x07, 0x09, 0x09, 0x23, 0x05, 0x52, 0x0F, 0x67, 0x2C, 0x11,

    WRITE_COMMAND_8, 0xB1,
    WRITE_BYTES, 16,
    0x0B, 0x11, 0x97, 0x0C, 0x12, 0x06, 0x06, 0x08, 0x08, 0x22, 0x03, 0x51, 0x11, 0x66, 0x2B, 0x0F,

    WRITE_COMMAND_8, 0xFF,
    WRITE_BYTES, 5,
    0x77, 0x01, 0x00, 0x00, 0x11,

    WRITE_C8_D8, 0xB0, 0x5D,
    WRITE_C8_D8, 0xB1, 0x2D,
    WRITE_C8_D8, 0xB2, 0x81,
    WRITE_C8_D8, 0xB3, 0x80,
    WRITE_C8_D8, 0xB5, 0x4E,
    WRITE_C8_D8, 0xB7, 0x85,
    WRITE_C8_D8, 0xB8, 0x20,
    WRITE_C8_D8, 0xC1, 0x78,
    WRITE_C8_D8, 0xC2, 0x78,
    WRITE_C8_D8, 0xD0, 0x88,

    WRITE_COMMAND_8, 0xE0,
    WRITE_BYTES, 3,
    0x00, 0x00, 0x02,

    WRITE_COMMAND_8, 0xE1,
    WRITE_BYTES, 11,
    0x06, 0x30, 0x08, 0x30, 0x05, 0x30, 0x07, 0x30, 0x00, 0x33, 0x33,

    WRITE_COMMAND_8, 0xE2,
    WRITE_BYTES, 12,
    0x11, 0x11, 0x33, 0x33, 0xF4, 0x00, 0x00, 0x00, 0xF4, 0x00, 0x00, 0x00,

    WRITE_COMMAND_8, 0xE3,
    WRITE_BYTES, 4,
    0x00, 0x00, 0x11, 0x11,

    WRITE_C8_D16, 0xE4, 0x44, 0x44,

    WRITE_COMMAND_8, 0xE5,
    WRITE_BYTES, 16,
    0x0D, 0xF5, 0x30, 0xF0, 0x0F, 0xF7, 0x30, 0xF0, 0x09, 0xF1, 0x30, 0xF0, 0x0B, 0xF3, 0x30, 0xF0,

    WRITE_COMMAND_8, 0xE6,
    WRITE_BYTES, 4,
    0x00, 0x00, 0x11, 0x11,

    WRITE_C8_D16, 0xE7, 0x44, 0x44,

    WRITE_COMMAND_8, 0xE8,
    WRITE_BYTES, 16,
    0x0C, 0xF4, 0x30, 0xF0, 0x0E, 0xF6, 0x30, 0xF0, 0x08, 0xF0, 0x30, 0xF0, 0x0A, 0xF2, 0x30, 0xF0,

    WRITE_C8_D16, 0xE9, 0x36, 0x01,

    WRITE_COMMAND_8, 0xEB,
    WRITE_BYTES, 7,
    0x00, 0x01, 0xE4, 0xE4, 0x44, 0x88, 0x40,

    WRITE_COMMAND_8, 0xED,
    WRITE_BYTES, 16,
    0xFF, 0x10, 0xAF, 0x76, 0x54, 0x2B, 0xCF, 0xFF, 0xFF, 0xFC, 0xB2, 0x45, 0x67, 0xFA, 0x01, 0xFF,

    WRITE_COMMAND_8, 0xEF,
    WRITE_BYTES, 6,
    0x08, 0x08, 0x08, 0x45, 0x3F, 0x54,

    WRITE_COMMAND_8, 0xFF,
    WRITE_BYTES, 5,
    0x77, 0x01, 0x00, 0x00, 0x00,

    WRITE_COMMAND_8, 0x11,

    END_WRITE,
    DELAY, 120,
    BEGIN_WRITE,

    WRITE_C8_D8, 0x3A, 0x66,
    WRITE_C8_D8, 0x36, 0x00,
    WRITE_C8_D8, 0x35, 0x00,

    WRITE_COMMAND_8, 0x29,
    END_WRITE,
    DELAY, 50};

// HD371001C40 3.71" bar display
//    1 /* hync_polarity */, 20 /* hsync_front_porch */, 8 /* hsync_pulse_width */, 20 /* hsync_back_porch */,
//    1 /* vsync_polarity */, 20 /* vsync_front_porch */, 8 /* vsync_pulse_width */, 20 /* vsync_back_porch, */,
//    0 /* pclk_active_neg */, GFX_NOT_DEFINED /* prefer_speed */, false /* useBigEndian */, 0 /* de_idle_high */,
//    0 /* pclk_idle_high */, 120 /* col_offset1 */ );
static const uint8_t HD371001C40_init_operations[] = {
    BEGIN_WRITE,
    WRITE_COMMAND_8, 0xFF,
    WRITE_BYTES, 5, 0x77, 0x01, 0x00, 0x00, 0x13,

    WRITE_C8_D8, 0xEF, 0x08,
    WRITE_COMMAND_8, 0xFF,
    WRITE_BYTES, 5, 0x77, 0x01, 0x00, 0x00, 0x10,

    WRITE_C8_D16, 0xC0, 0x77, 0x00,
    WRITE_C8_D16, 0xC1, 0x11, 0x0C,
    WRITE_C8_D16, 0xC2, 0x07, 0x02,
    WRITE_C8_D8, 0xCC, 0x30,
    WRITE_COMMAND_8, 0xB0,
    WRITE_BYTES, 16, 0x06, 0xCF, 0x14, 0x0C, 0x0F, 0x03, 0x00, 0x0A, 0x07, 0x1B, 0x03, 0x12, 0x10, 0x25, 0x36, 0x1E,

    WRITE_COMMAND_8, 0xB1,
    WRITE_BYTES, 16, 0x0C, 0xD4, 0x18, 0x0C, 0x0E, 0x06, 0x03, 0x06, 0x08, 0x23, 0x06, 0x12, 0x10, 0x30, 0x2F, 0x1F,

    WRITE_COMMAND_8, 0xFF,
    WRITE_BYTES, 5, 0x77, 0x01, 0x00, 0x00, 0x11,

    WRITE_C8_D8, 0xB0, 0x73,
    WRITE_C8_D8, 0xB1, 0x7C,
    WRITE_C8_D8, 0xB2, 0x83,
    WRITE_C8_D8, 0xB3, 0x80,
    WRITE_C8_D8, 0xB5, 0x49,
    WRITE_C8_D8, 0xB7, 0x87,
    WRITE_C8_D8, 0xB8, 0x33,
    WRITE_C8_D16, 0xB9, 0x10, 0x1F,
    WRITE_C8_D8, 0xBB, 0x03,
    WRITE_C8_D8, 0xC1, 0x08,
    WRITE_C8_D8, 0xC2, 0x08,
    WRITE_C8_D8, 0xD0, 0x88,
    WRITE_COMMAND_8, 0xE0,
    WRITE_BYTES, 6, 0x00, 0x00, 0x02, 0x00, 0x00, 0x0C,

    WRITE_COMMAND_8, 0xE1,
    WRITE_BYTES, 11, 0x05, 0x96, 0x07, 0x96, 0x06, 0x96, 0x08, 0x96, 0x00, 0x44, 0x44,

    WRITE_COMMAND_8, 0xE2,
    WRITE_BYTES, 12, 0x00, 0x00, 0x03, 0x03, 0x00, 0x00, 0x02, 0x00, 0x00, 0x00, 0x02, 0x00,

    WRITE_COMMAND_8, 0xE3,
    WRITE_BYTES, 4, 0x00, 0x00, 0x33, 0x33,

    WRITE_C8_D16, 0xE4, 0x44, 0x44,
    WRITE_COMMAND_8, 0xE5,
    WRITE_BYTES, 16, 0x0D, 0xD4, 0x28, 0x8C, 0x0F, 0xD6, 0x28, 0x8C, 0x09, 0xD0, 0x28, 0x8C, 0x0B, 0xD2, 0x28, 0x8C,

    WRITE_COMMAND_8, 0xE6,
    WRITE_BYTES, 4, 0x00, 0x00, 0x33, 0x33,

    WRITE_C8_D16, 0xE7, 0x44, 0x44,
    WRITE_COMMAND_8, 0xE8,
    WRITE_BYTES, 16, 0x0E, 0xD5, 0x28, 0x8C, 0x10, 0xD7, 0x28, 0x8C, 0x0A, 0xD1, 0x28, 0x8C, 0x0C, 0xD3, 0x28, 0x8C,

    WRITE_COMMAND_8, 0xEB,
    WRITE_BYTES, 6, 0x00, 0x01, 0xE4, 0xE4, 0x44, 0x00,

    WRITE_COMMAND_8, 0xED,
    WRITE_BYTES, 16, 0xF3, 0xC1, 0xBA, 0x0F, 0x66, 0x77, 0x44, 0x55, 0x55, 0x44, 0x77, 0x66, 0xF0, 0xAB, 0x1C, 0x3F,

    WRITE_COMMAND_8, 0xEF,
    WRITE_BYTES, 6, 0x10, 0x0D, 0x04, 0x08, 0x3F, 0x1F,

    WRITE_COMMAND_8, 0xFF,
    WRITE_BYTES, 5, 0x77, 0x01, 0x00, 0x00, 0x13,

    WRITE_C8_D16, 0xE8, 0x00, 0x0E,
    WRITE_COMMAND_8, 0x11,
    END_WRITE,
    DELAY, 0x78,
    BEGIN_WRITE,
    WRITE_C8_D16, 0xE8, 0x00, 0x0C,
    END_WRITE,
    DELAY, 0x0A,
    BEGIN_WRITE,
    WRITE_C8_D16, 0xE8, 0x40, 0x00,
    WRITE_COMMAND_8, 0xFF,
    WRITE_BYTES, 5, 0x77, 0x01, 0x00, 0x00, 0x00,

    WRITE_C8_D8, 0x36, 0x00,
    WRITE_C8_D8, 0x3A, 0x66,
    WRITE_COMMAND_8, 0x29,
    END_WRITE,
    DELAY, 0x14,
    BEGIN_WRITE,
    WRITE_COMMAND_8, 0xFF,
    WRITE_BYTES, 5, 0x77, 0x01, 0x00, 0x00, 0x10,

    WRITE_C8_D16, 0xE5, 0x00, 0x00};

// HD458002C40 4.58" bar display
//    1 /* hync_polarity */, 10 /* hsync_front_porch */, 10 /* hsync_pulse_width */, 50 /* hsync_back_porch */,
//    1 /* vsync_polarity */, 15 /* vsync_front_porch */, 2 /* vsync_pulse_width */, 17 /* vsync_back_porch */,
//    1 /* pclk_active_neg */, GFX_NOT_DEFINED /* prefer_speed */, false /* useBigEndian */, 0 /* de_idle_high */,
//    0 /* pclk_idle_high */, 80 /* col_offset */, 0 /* row_offset1 */, 8 /* col_offset2 */ );
static const uint8_t HD458002C40_init_operations[] = {
    BEGIN_WRITE,
    WRITE_COMMAND_8, 0xFF,
    WRITE_BYTES, 5, 0x77, 0x01, 0x00, 0x00, 0x13,

    WRITE_C8_D8, 0xEF, 0x08,
    WRITE_COMMAND_8, 0xFF,
    WRITE_BYTES, 5, 0x77, 0x01, 0x00, 0x00, 0x10,

    WRITE_C8_D16, 0xC0, 0x77, 0x00,
    WRITE_C8_D16, 0xC1, 0x09, 0x08,
    WRITE_C8_D16, 0xC2, 0x01, 0x02,
    WRITE_C8_D8, 0xC3, 0x02,
    WRITE_C8_D8, 0xCC, 0x10,
    WRITE_COMMAND_8, 0xB0,
    WRITE_BYTES, 16, 0x40, 0x14, 0x59, 0x10, 0x12, 0x08, 0x03, 0x09, 0x05, 0x1E, 0x05, 0x14, 0x10, 0x68, 0x33, 0x15,

    WRITE_COMMAND_8, 0xB1,
    WRITE_BYTES, 16, 0x40, 0x08, 0x53, 0x09, 0x11, 0x09, 0x02, 0x07, 0x09, 0x1A, 0x04, 0x12, 0x12, 0x64, 0x29, 0x29,

    WRITE_COMMAND_8, 0xFF,
    WRITE_BYTES, 5, 0x77, 0x01, 0x00, 0x00, 0x11,

    WRITE_C8_D8, 0xB0, 0x6D,
    WRITE_C8_D8, 0xB1, 0x1D,
    WRITE_C8_D8, 0xB2, 0x87,
    WRITE_C8_D8, 0xB3, 0x80,
    WRITE_C8_D8, 0xB5, 0x49,
    WRITE_C8_D8, 0xB7, 0x85,
    WRITE_C8_D8, 0xB8, 0x20,
    WRITE_C8_D8, 0xC1, 0x78,
    WRITE_C8_D8, 0xC2, 0x78,
    WRITE_C8_D8, 0xD0, 0x88,
    WRITE_COMMAND_8, 0xE0,
    WRITE_BYTES, 3, 0x00, 0x00, 0x02,

    WRITE_COMMAND_8, 0xE1,
    WRITE_BYTES, 11, 0x02, 0x8C, 0x00, 0x00, 0x03, 0x8C, 0x00, 0x00, 0x00, 0x33, 0x33,

    WRITE_COMMAND_8, 0xE2,
    WRITE_BYTES, 13, 0x33, 0x33, 0x33, 0x33, 0xC9, 0x3C, 0x00, 0x00, 0xCA, 0x3C, 0x00, 0x00, 0x00,

    WRITE_COMMAND_8, 0xE3,
    WRITE_BYTES, 4, 0x00, 0x00, 0x33, 0x33,

    WRITE_C8_D16, 0xE4, 0x44, 0x44,
    WRITE_COMMAND_8, 0xE5,
    WRITE_BYTES, 16, 0x05, 0xCD, 0x82, 0x82, 0x01, 0xC9, 0x82, 0x82, 0x07, 0xCF, 0x82, 0x82, 0x03, 0xCB, 0x82, 0x82,

    WRITE_COMMAND_8, 0xE6,
    WRITE_BYTES, 4, 0x00, 0x00, 0x33, 0x33,

    WRITE_C8_D16, 0xE7, 0x44, 0x44,
    WRITE_COMMAND_8, 0xE8,
    WRITE_BYTES, 16, 0x06, 0xCE, 0x82, 0x82, 0x02, 0xCA, 0x82, 0x82, 0x08, 0xD0, 0x82, 0x82, 0x04, 0xCC, 0x82, 0x82,

    WRITE_COMMAND_8, 0xEB,
    WRITE_BYTES, 7, 0x08, 0x01, 0xE4, 0xE4, 0x88, 0x00, 0x40,

    WRITE_COMMAND_8, 0xEC,
    WRITE_BYTES, 3, 0x00, 0x00, 0x00,

    WRITE_COMMAND_8, 0xED,
    WRITE_BYTES, 16, 0xFF, 0xF0, 0x07, 0x65, 0x4F, 0xFC, 0xC2, 0x2F, 0xF2, 0x2C, 0xCF, 0xF4, 0x56, 0x70, 0x0F, 0xFF,

    WRITE_COMMAND_8, 0xEF,
    WRITE_BYTES, 6, 0x10, 0x0D, 0x04, 0x08, 0x3F, 0x1F,

    WRITE_COMMAND_8, 0xFF,
    WRITE_BYTES, 5, 0x77, 0x01, 0x00, 0x00, 0x00,

    WRITE_COMMAND_8, 0x11,
    END_WRITE,
    DELAY, 0x78,
    BEGIN_WRITE,
    WRITE_C8_D8, 0x35, 0x00,
    WRITE_C8_D8, 0x3A, 0x66,
    WRITE_COMMAND_8, 0x29};

class Arduino_RGB_Display : public Arduino_GFX
{
public:
    Arduino_RGB_Display(
        int16_t w, int16_t h, Arduino_ESP32RGBPanel *rgbpanel, uint8_t r = 0, bool auto_flush = true,
        Arduino_DataBus *bus = NULL, int8_t rst = GFX_NOT_DEFINED, const uint8_t *init_operations = NULL, size_t init_operations_len = GFX_NOT_DEFINED,
        uint8_t col_offset1 = 0, uint8_t row_offset1 = 0, uint8_t col_offset2 = 0, uint8_t row_offset2 = 0);

    bool begin(int32_t speed = GFX_NOT_DEFINED) override;
    void writePixelPreclipped(int16_t x, int16_t y, uint16_t color) override;
    void writeFastVLine(int16_t x, int16_t y, int16_t h, uint16_t color) override;
    void writeFastVLineCore(int16_t x, int16_t y, int16_t h, uint16_t color);
    void writeFastHLine(int16_t x, int16_t y, int16_t w, uint16_t color) override;
    void writeFastHLineCore(int16_t x, int16_t y, int16_t w, uint16_t color);
    void writeFillRectPreclipped(int16_t x, int16_t y, int16_t w, int16_t h, uint16_t color) override;
    void drawIndexedBitmap(int16_t x, int16_t y, uint8_t *bitmap, uint16_t *color_index, int16_t w, int16_t h, int16_t x_skip = 0) override;
    void draw16bitRGBBitmap(int16_t x, int16_t y, uint16_t *bitmap, int16_t w, int16_t h) override;
    void draw16bitBeRGBBitmap(int16_t x, int16_t y, uint16_t *bitmap, int16_t w, int16_t h) override;
    void flush(bool force_flush = false) override;

    void drawYCbCrBitmap(int16_t x, int16_t y, uint8_t *yData, uint8_t *cbData, uint8_t *crData, int16_t w, int16_t h);
    uint16_t *getFramebuffer();
    uint16_t *getFramebuffer2();
    esp_lcd_panel_handle_t getRgbPanelHandle();

protected:
    uint16_t *_framebuffer;
    size_t _framebuffer_size;
    Arduino_ESP32RGBPanel *_rgbpanel;
    bool _auto_flush;
    Arduino_DataBus *_bus;
    int8_t _rst;
    const uint8_t *_init_operations;
    size_t _init_operations_len;
    int16_t MAX_X, MAX_Y;
    uint8_t COL_OFFSET1, ROW_OFFSET1;
    uint8_t COL_OFFSET2, ROW_OFFSET2;
    uint8_t _xStart, _yStart;
    uint16_t _fb_width, _fb_height, _fb_max_x, _fb_max_y;

private:
};

#endif // #if defined(ESP32) && (CONFIG_IDF_TARGET_ESP32S3)
