G-districts/CrowPanel-7.0-HMI-ESP32-Display-800x480/example/V1.0_and_V2.0/Micropython/CrowPanel-7.0-MicroPython/Examples/play_tone.py

import os
import math
import struct
from machine import I2S
from machine import Pin

def make_tone(rate, bits, frequency):
    # create a buffer containing the pure tone samples
    samples_per_cycle = rate // frequency
    sample_size_in_bytes = bits // 8
    samples = bytearray(samples_per_cycle * sample_size_in_bytes)
    volume_reduction_factor = 32
    range = pow(2, bits) // 2 // volume_reduction_factor
    
    if bits == 16:
        format = "<h"
    else:  # assume 32 bits
        format = "<l"
    
    for i in range(samples_per_cycle):
        sample = range + int((range - 1) * math.sin(2 * math.pi * i / samples_per_cycle))
        struct.pack_into(format, samples, i * sample_size_in_bytes, sample)
        
    return samples

if os.uname().machine.count("PYBv1"):

    # ======= I2S CONFIGURATION =======
    SCK_PIN = "Y6"
    WS_PIN = "Y5"
    SD_PIN = "Y8"
    I2S_ID = 2
    BUFFER_LENGTH_IN_BYTES = 2000
    # ======= I2S CONFIGURATION =======

elif os.uname().machine.count("PYBD"):
    import pyb

    pyb.Pin("EN_3V3").on()  # provide 3.3V on 3V3 output pin

    # ======= I2S CONFIGURATION =======
    SCK_PIN = "Y6"
    WS_PIN = "Y5"
    SD_PIN = "Y8"
    I2S_ID = 2
    BUFFER_LENGTH_IN_BYTES = 2000
    # ======= I2S CONFIGURATION =======

elif os.uname().machine.count("ESP32"):

    # ======= I2S CONFIGURATION =======
    SCK_PIN = 42
    WS_PIN = 18
    SD_PIN = 17
    I2S_ID = 0
    BUFFER_LENGTH_IN_BYTES = 2000
    # ======= I2S CONFIGURATION =======

elif os.uname().machine.count("Raspberry"):

    # ======= I2S CONFIGURATION =======
    SCK_PIN = 16
    WS_PIN = 17
    SD_PIN = 18
    I2S_ID = 0
    BUFFER_LENGTH_IN_BYTES = 1000
    # ======= I2S CONFIGURATION =======

elif os.uname().machine.count("MIMXRT"):

    # ======= I2S CONFIGURATION =======
    SCK_PIN = 4
    WS_PIN = 3
    SD_PIN = 2
    I2S_ID = 2
    BUFFER_LENGTH_IN_BYTES = 2000
    # ======= I2S CONFIGURATION =======

else:
    print("Warning: program not tested with this board")

# ======= AUDIO CONFIGURATION =======
TONE_FREQUENCY_IN_HZ = 440
SAMPLE_SIZE_IN_BITS = 16
FORMAT = I2S.MONO  # only MONO supported in this example
SAMPLE_RATE_IN_HZ = 22_050
# ======= AUDIO CONFIGURATION =======

audio_out = I2S(
    I2S_ID,
    sck=Pin(SCK_PIN),
    ws=Pin(WS_PIN),
    sd=Pin(SD_PIN),
    mode=I2S.TX,
    bits=SAMPLE_SIZE_IN_BITS,
    format=FORMAT,
    rate=SAMPLE_RATE_IN_HZ,
    ibuf=BUFFER_LENGTH_IN_BYTES,
)

samples = make_tone(SAMPLE_RATE_IN_HZ, SAMPLE_SIZE_IN_BITS, TONE_FREQUENCY_IN_HZ)

# continuously write tone sample buffer to an I2S DAC
print("==========  START PLAYBACK ==========")
try:
    while True:
        num_written = audio_out.write(samples)

except (KeyboardInterrupt, Exception) as e:
    print("caught exception {} {}".format(type(e).__name__, e))

# cleanup
audio_out.deinit()
print("Done")
