G-districts/CrowPanel-7.0-HMI-ESP32-Display-800x480/example/V1.0_and_V2.0/Micropython/CrowPanel-7.0-MicroPython/Examples/wifi.py

import network
import time

def connect():
    ssid = 'yanfa_software'
    password = 'yanfa-123456'
    
    wlan = network.WLAN(network.STA_IF)  # Create a WLAN object in station mode
    wlan.active(True)  # Activate the network interface
    wlan.connect(ssid, password)  # Connect to the specified WiFi network
    
    while not wlan.isconnected():  # Wait for the connection to be established
        print('Waiting for connection...')
        time.sleep(1)
    
    print('Connected on {ip}'.format(ip=wlan.ifconfig()[0]))  # Print the IP address

connect()
